0sleep/lwLIDAR/Firmware/components/thesis/include/networking.h

// networking.h
#pragma once

#include "esp_err.h"
#include "esp_log.h"

#include "nvs_flash.h"
#include "esp_event.h"
#include "esp_wifi.h"

#include "freertos/FreeRTOS.h"

esp_err_t networking_init(void);

esp_err_t networking_connect(char* wifi_ssid, char* wifi_password);

esp_err_t networking_disconnect(void);

esp_err_t networking_deinit(void);
